KyleV1999/LumiMonitor/Images/box_top_cropped.jpg

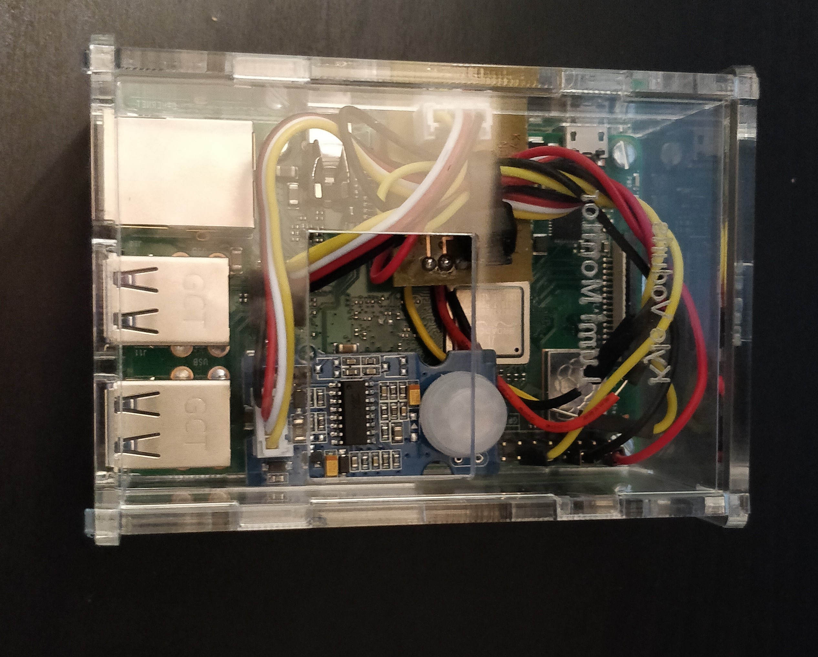
Images/box_top_cropped.jpg
