KyleV1999/LumiMonitor/Images/grovesensor.jpg

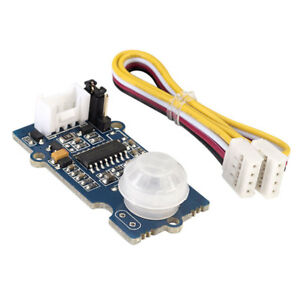
Images/grovesensor.jpg
