KyleV1999/LumiMonitor/Images/Lumi_Monitor_Schedual_1.JPG

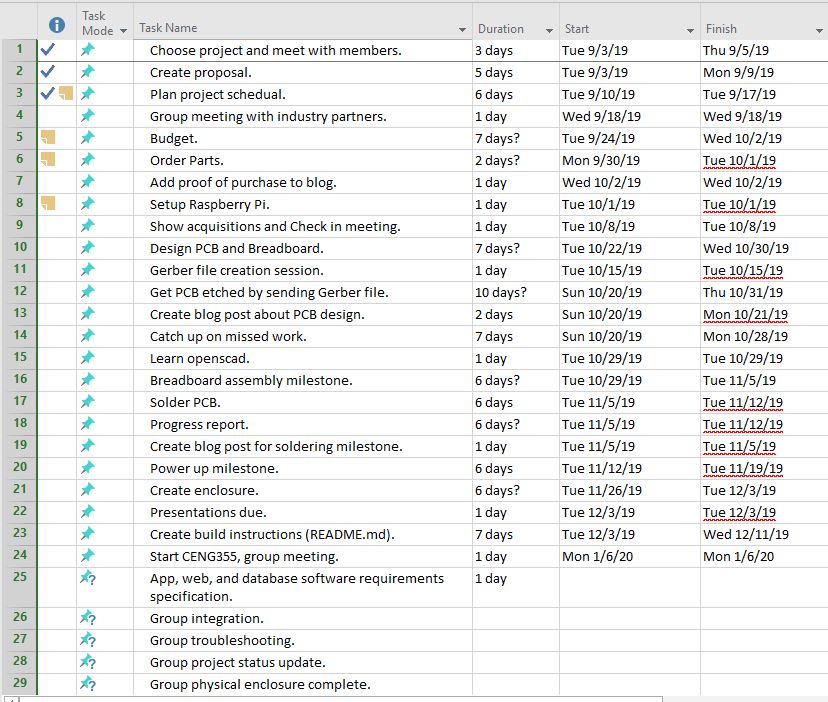
Images/Lumi_Monitor_Schedual_1.JPG
