KyleV1999/LumiMonitor/Images/pcb_front_cropped.jpg

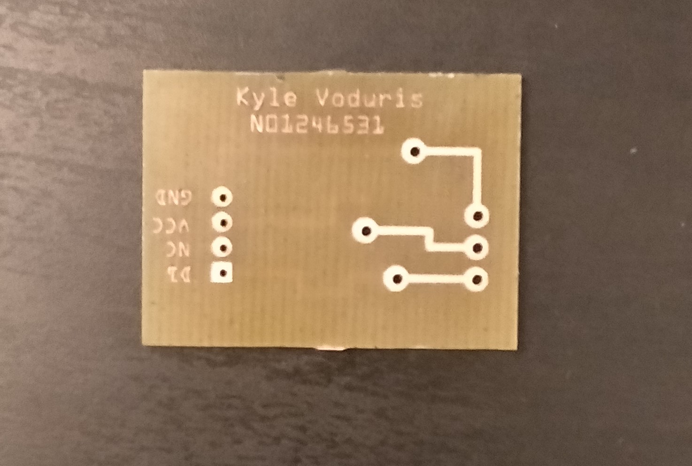
Images/pcb_front_cropped.jpg
