KyleV1999/LumiMonitor/Images/RD1.PNG

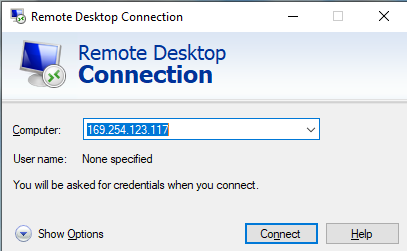
Images/RD1.PNG
