KyleV1999/LumiMonitor/Images/RD2.PNG

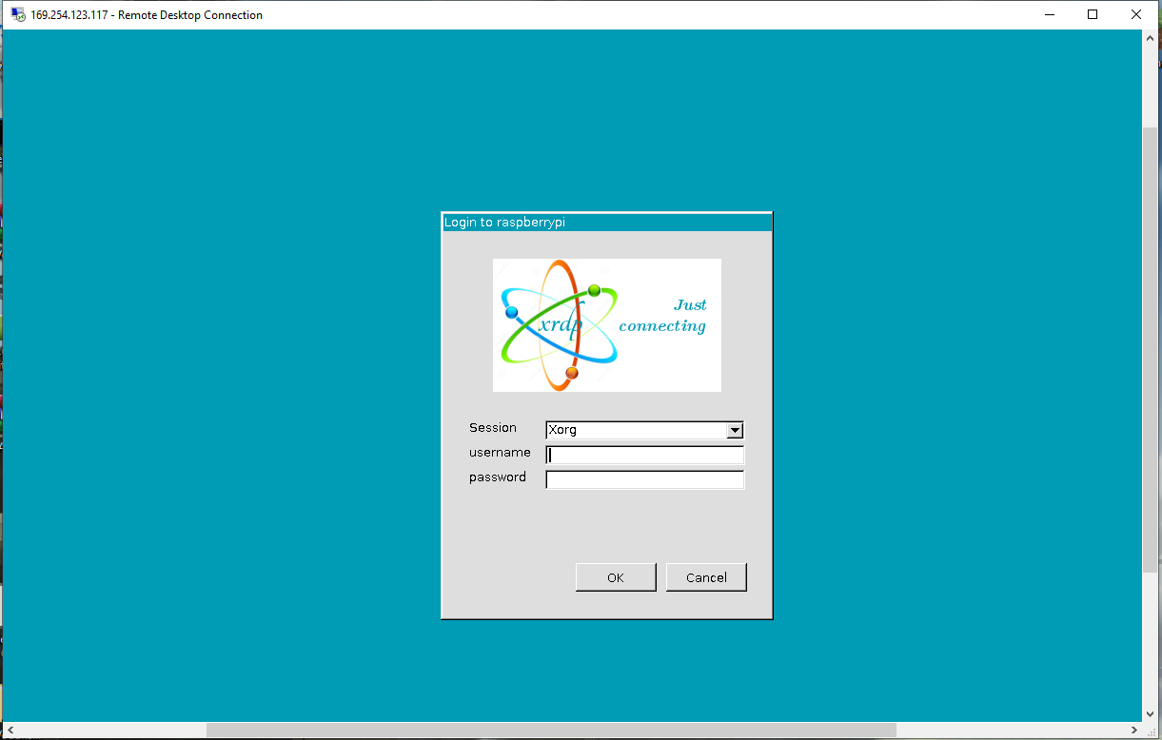
Images/RD2.PNG
