KyleV1999/LumiMonitor/Images/RD3.PNG

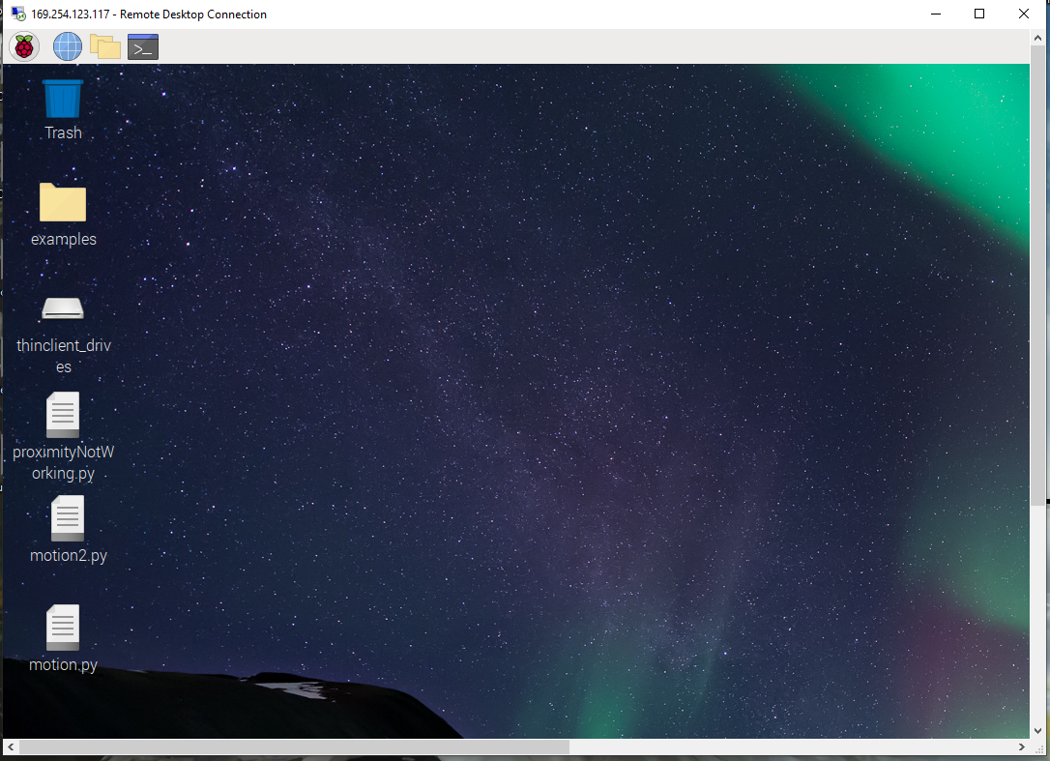
Images/RD3.PNG
