KyleV1999/LumiMonitor/Images/ScreenCapture2.JPG

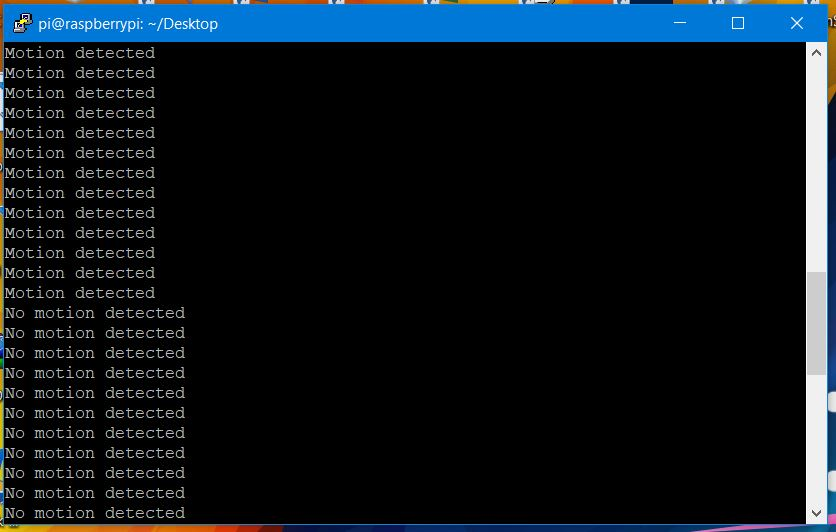
Images/ScreenCapture2.JPG
